HugoMarkoff/Insect_detector/hardware/cad/TEST/New-PIR/PIRbracket.3MF

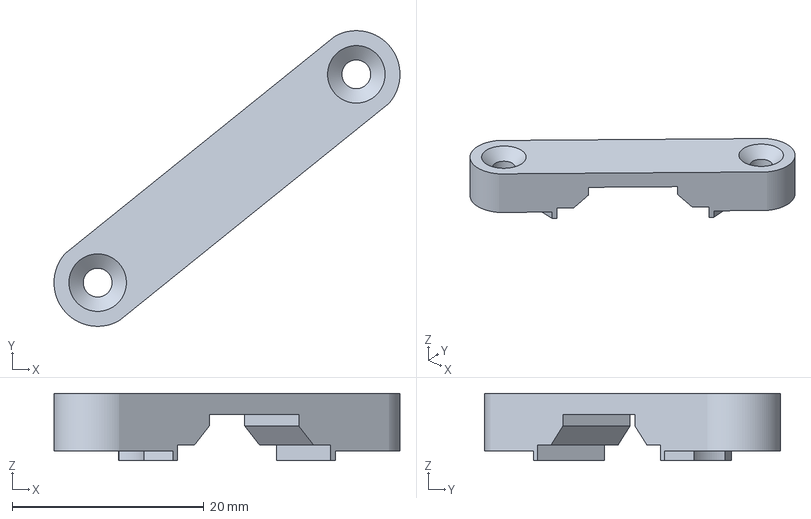
[picture p21: CAD file, 2026-08-19]
hardware/cad/TEST/New-PIR/PIRbracket.3MF
36.1 x 30.9 x 7.00 mm
