HugoMarkoff/Insect_detector/hardware/cad/Shade.3MF

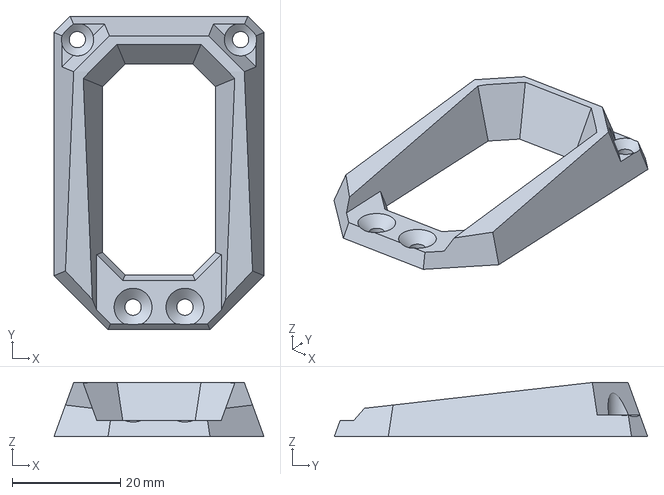
[picture p22: CAD file, 2026-08-19]
hardware/cad/Shade.3MF
38.9 x 58.0 x 10.0 mm
