HugoMarkoff/Insect_detector/hardware/cad/TEST/Back-shell.3MF

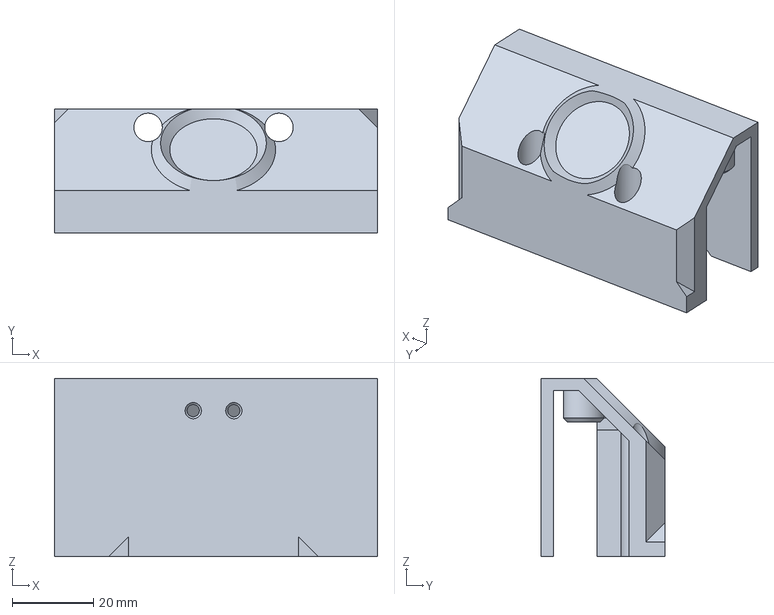
[picture p23: CAD file, 2026-08-19]
hardware/cad/TEST/Back-shell.3MF
79.6 x 30.5 x 44.0 mm
