HugoMarkoff/Insect_detector/hardware/cad/AntennaSafeInsert.3MF

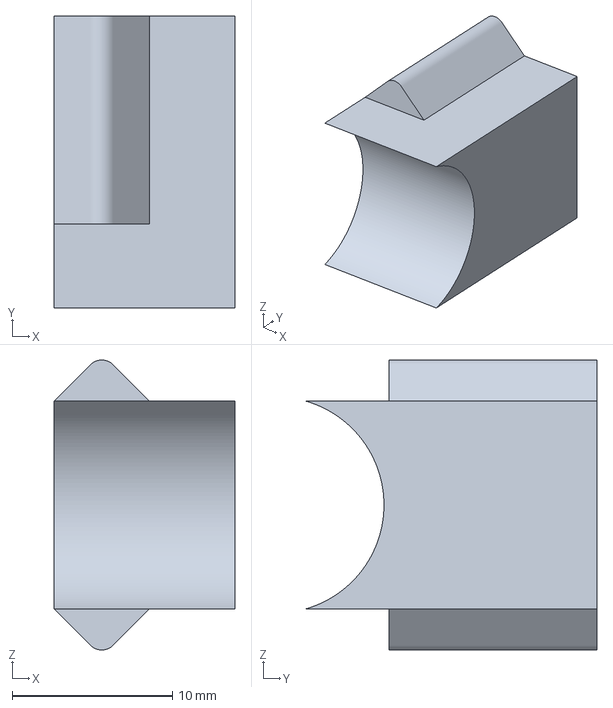
[picture p24: CAD file, 2026-08-19]
hardware/cad/AntennaSafeInsert.3MF
11.3 x 18.2 x 18.1 mm
