HugoMarkoff/Insect_detector/hardware/cad/TEST/Front-shell.3MF

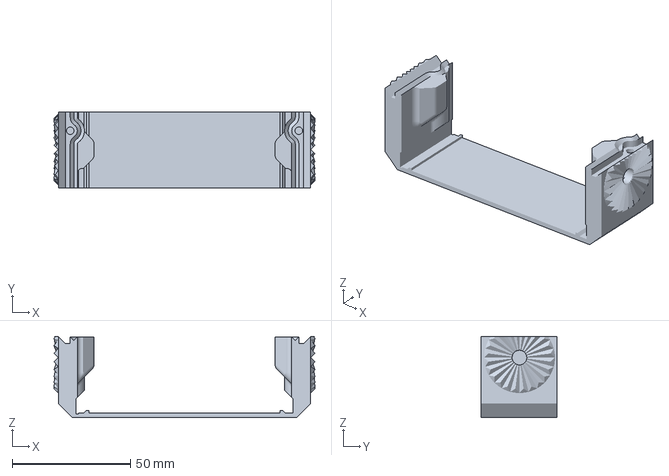
[picture p25: CAD file, 2026-08-19]
hardware/cad/TEST/Front-shell.3MF
110.5 x 32.3 x 34.4 mm
