HugoMarkoff/Insect_detector/hardware/cad/Bracket.3MF

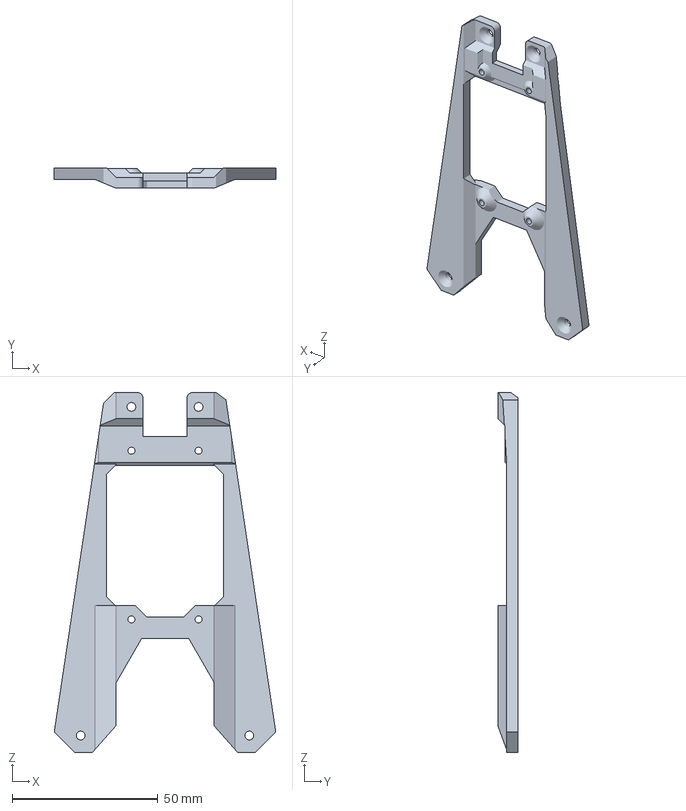
[picture p26: CAD file, 2026-08-19]
hardware/cad/Bracket.3MF
75.9 x 7.00 x 123.3 mm
