HugoMarkoff/Insect_detector/hardware/cad/TEST/PET-TEST.3MF

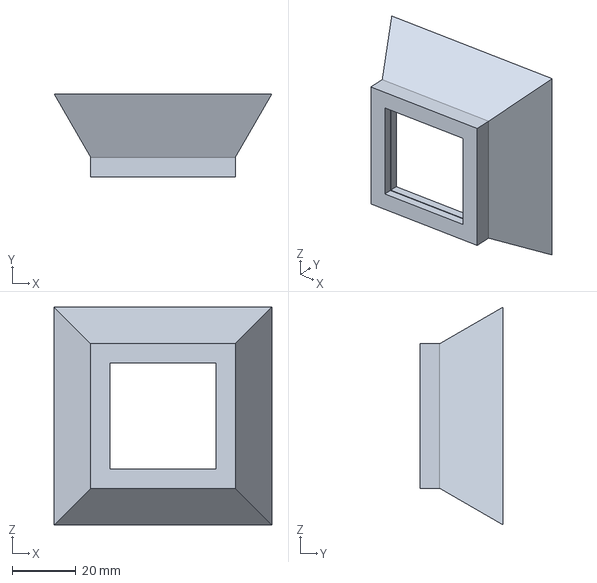
[picture p27: CAD file, 2026-08-19]
hardware/cad/TEST/PET-TEST.3MF
68.6 x 26.2 x 68.6 mm
