HugoMarkoff/Insect_detector/hardware/cad/Tree-Knob.3MF

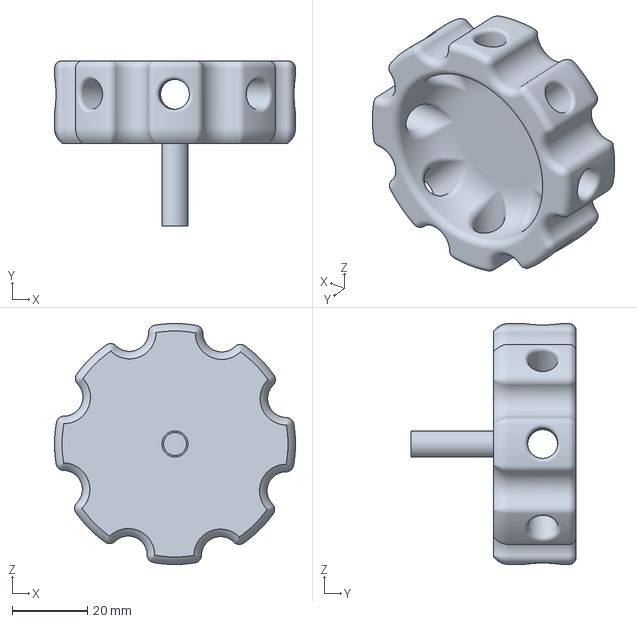
[picture p28: CAD file, 2026-08-19]
hardware/cad/Tree-Knob.3MF
64.0 x 43.9 x 64.0 mm
