HugoMarkoff/Insect_detector/hardware/cad/Shade - Big.3MF

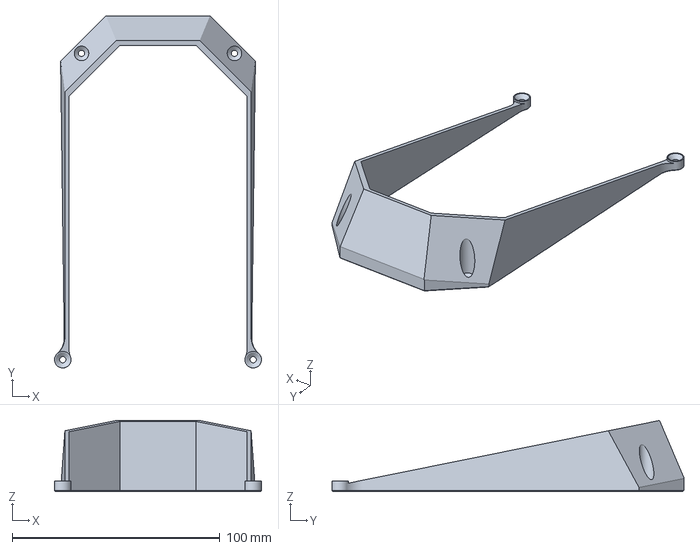
[picture p29: CAD file, 2026-08-19]
hardware/cad/Shade - Big.3MF
99.7 x 169.6 x 34.2 mm
