HugoMarkoff/Insect_detector/hardware/cad/IR-Insert-Folding.3MF

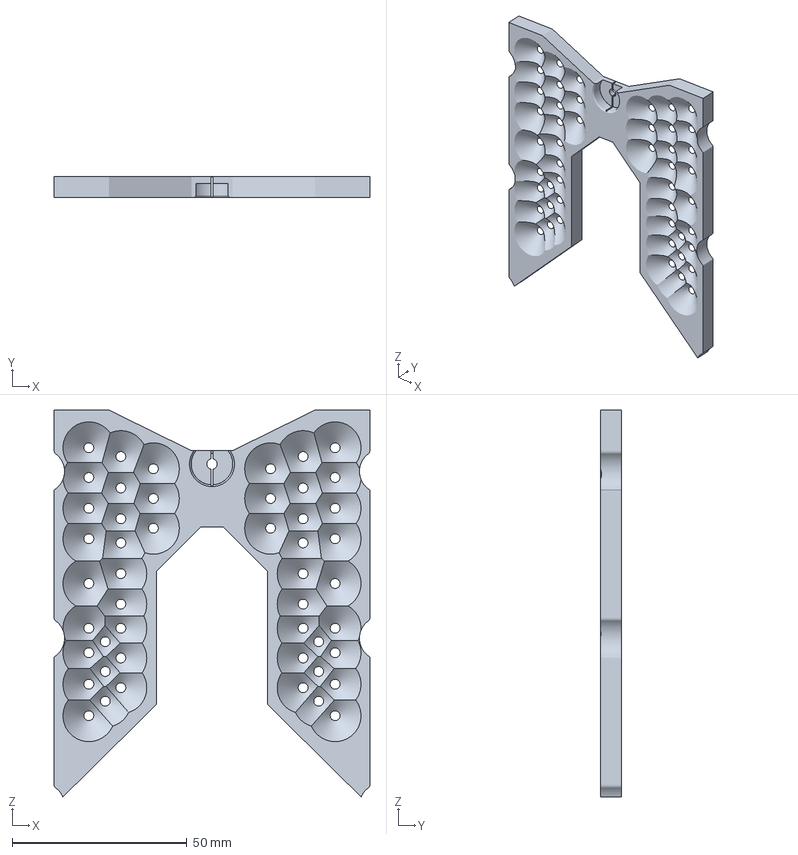
[picture p30: CAD file, 2026-08-19]
hardware/cad/IR-Insert-Folding.3MF
90.3 x 6.00 x 110.6 mm
