HugoMarkoff/Insect_detector/hardware/cad/AntennaSafeTip.3MF

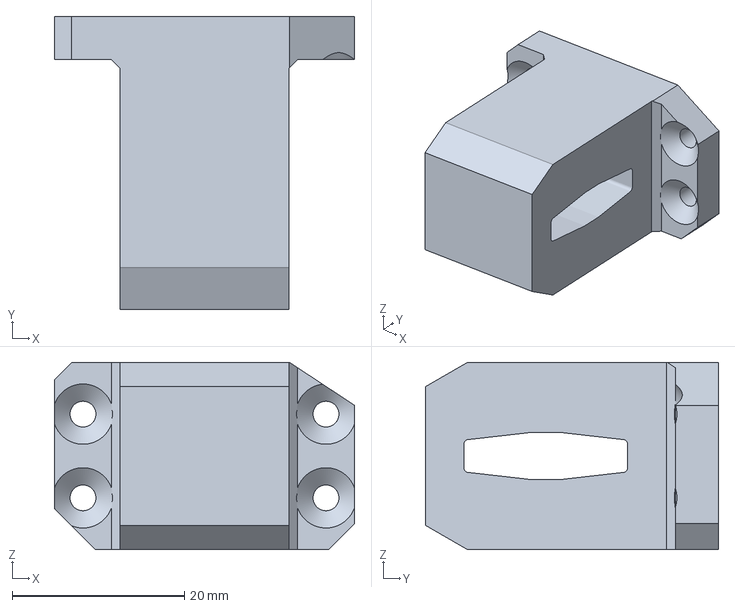
[picture p31: CAD file, 2026-08-19]
hardware/cad/AntennaSafeTip.3MF
34.9 x 34.0 x 21.7 mm
