HugoMarkoff/Insect_detector/hardware/cad/Back-shell.3MF

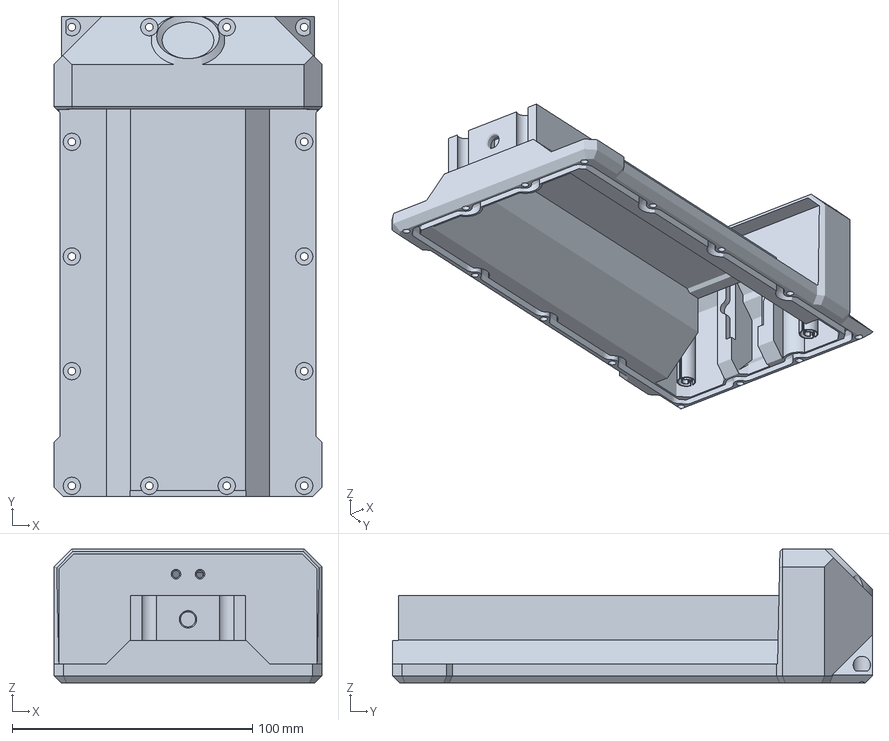
[picture p32: CAD file, 2026-08-19]
hardware/cad/Back-shell.3MF
111.6 x 200.0 x 55.8 mm
