HugoMarkoff/Insect_detector/hardware/cad/AntennaSafe.3MF

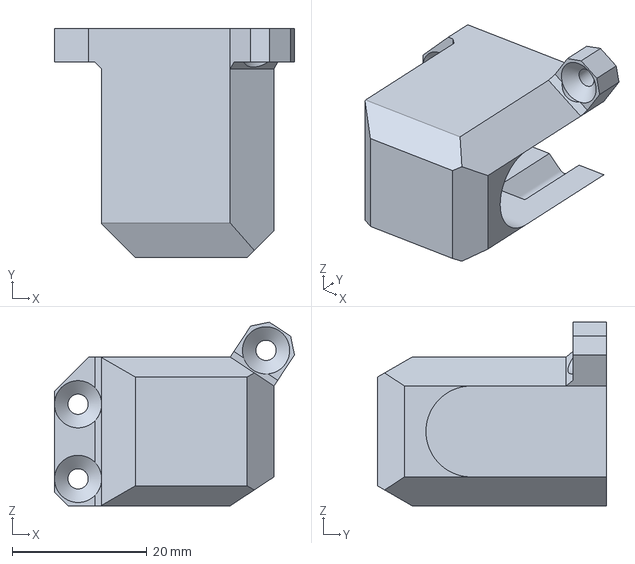
[picture p33: CAD file, 2026-08-19]
hardware/cad/AntennaSafe.3MF
35.6 x 34.0 x 27.3 mm
