HugoMarkoff/Insect_detector/hardware/cad/Charger-Top.3MF

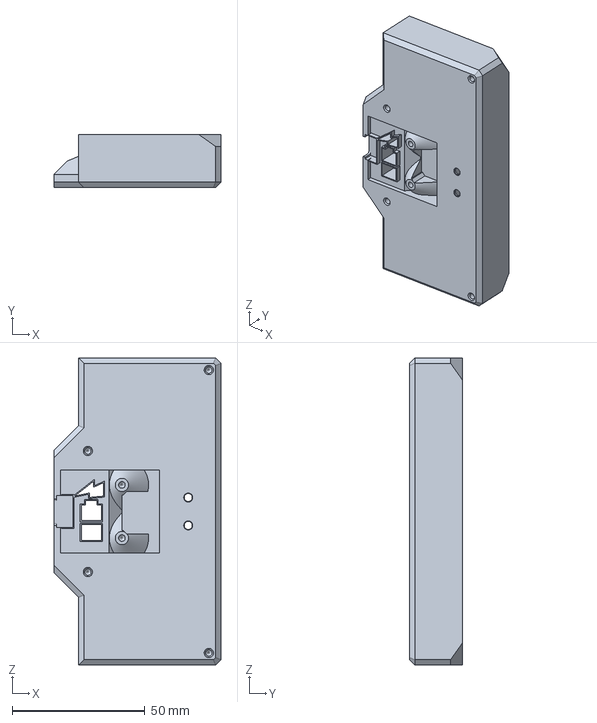
[picture p34: CAD file, 2026-08-19]
hardware/cad/Charger-Top.3MF
62.8 x 20.0 x 115.6 mm
