HugoMarkoff/Insect_detector/hardware/cad/Cam-Insert.3MF

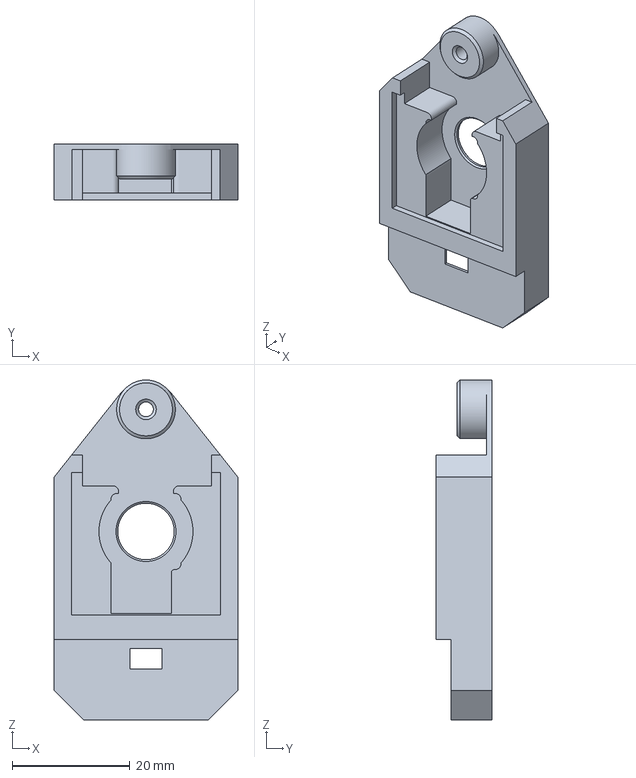
[picture p35: CAD file, 2026-08-19]
hardware/cad/Cam-Insert.3MF
31.3 x 9.60 x 57.9 mm
