HugoMarkoff/Insect_detector/hardware/cad/Charger-buttom.3MF

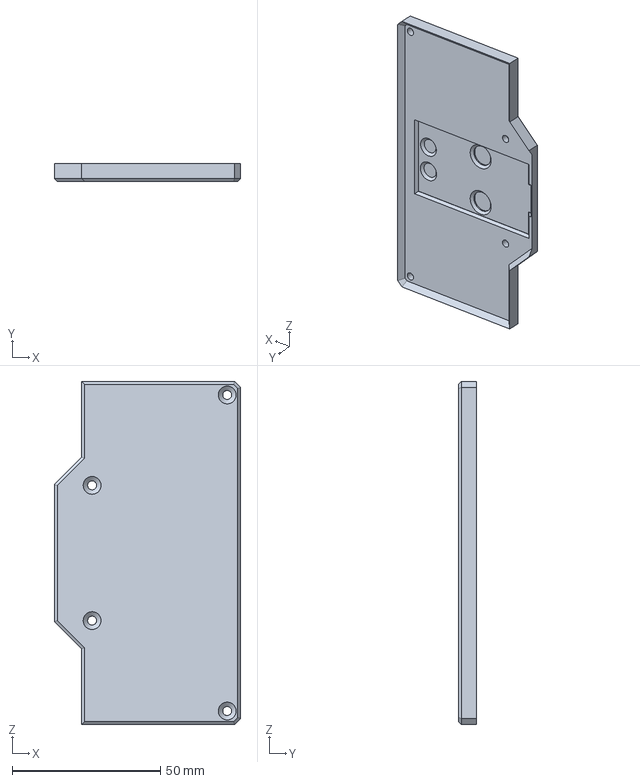
[picture p36: CAD file, 2026-08-19]
hardware/cad/Charger-buttom.3MF
62.8 x 6.10 x 115.6 mm
