HugoMarkoff/Insect_detector/hardware/cad/Front-shell.3MF

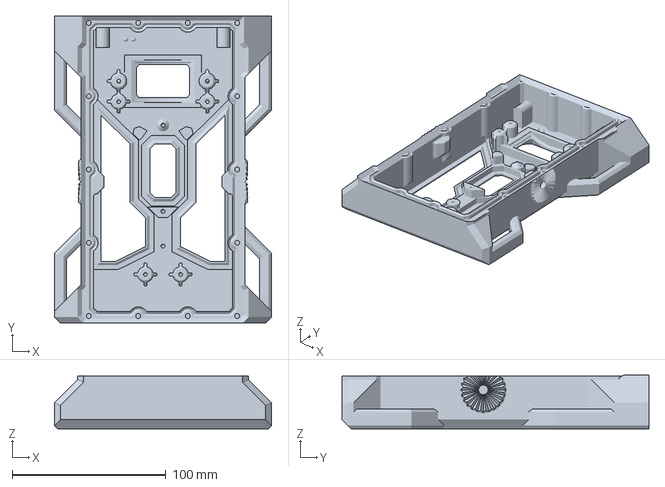
[picture p37: CAD file, 2026-08-19]
hardware/cad/Front-shell.3MF
141.6 x 200.0 x 34.9 mm
