HugoMarkoff/Insect_detector/hardware/cad/Battery-Knob.3MF

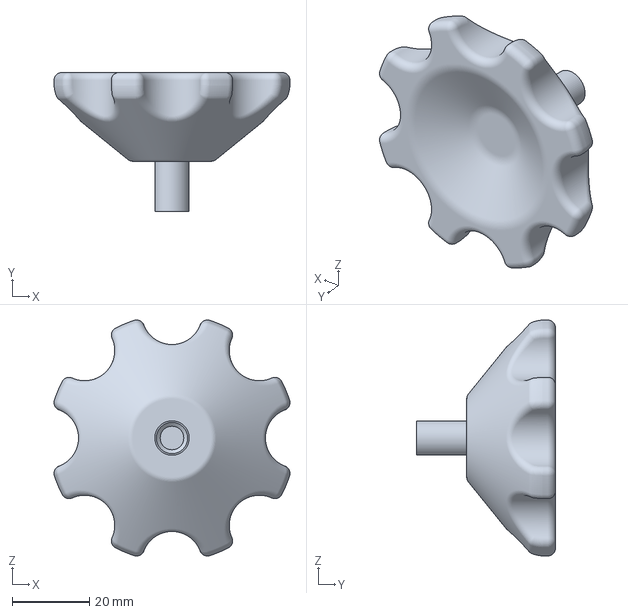
[picture p38: CAD file, 2026-08-19]
hardware/cad/Battery-Knob.3MF
61.1 x 36.0 x 61.1 mm
