HugoMarkoff/Insect_detector/hardware/cad/TreeBracket.3MF

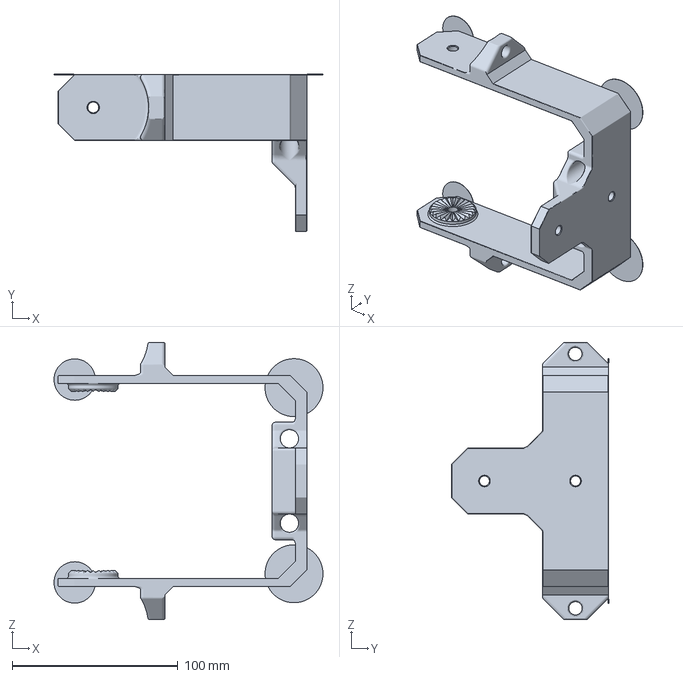
[picture p39: CAD file, 2026-08-19]
hardware/cad/TreeBracket.3MF
162.4 x 95.0 x 167.5 mm
