HugoMarkoff/Insect_detector/hardware/cad/Battery_Buttom.3MF

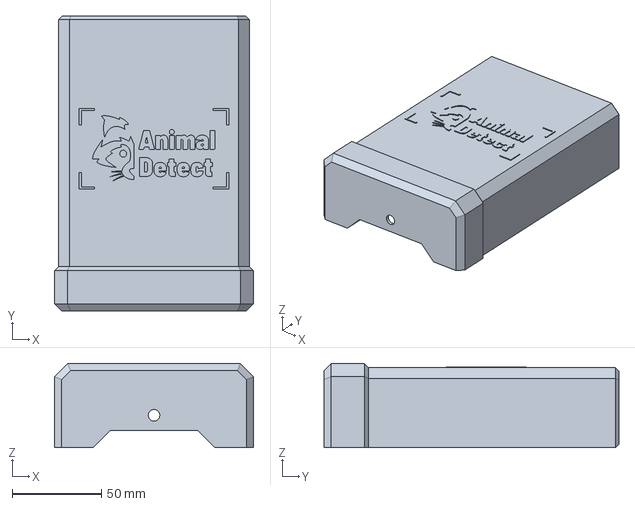
[picture p40: CAD file, 2026-08-19]
hardware/cad/Battery_Buttom.3MF
111.6 x 165.3 x 47.2 mm
